MOSH-Insa-Toulouse/2025-2026-4GP-CHAUPIN-ADJASSE/LTSPICE/symb_ampli.png

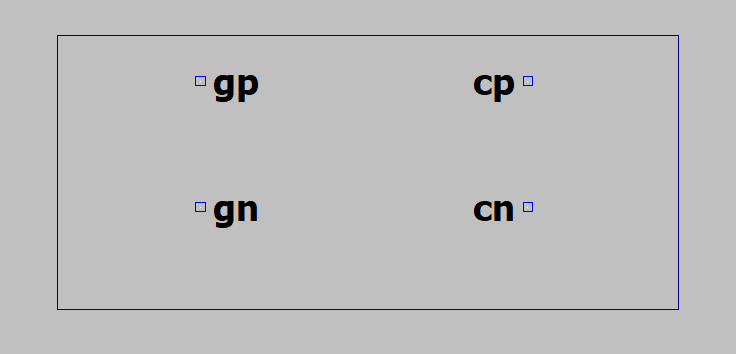
LTSPICE/symb_ampli.png
