MOSH-Insa-Toulouse/2025-2026-4GP-CHAUPIN-ADJASSE/LTSPICE/symb_full.png

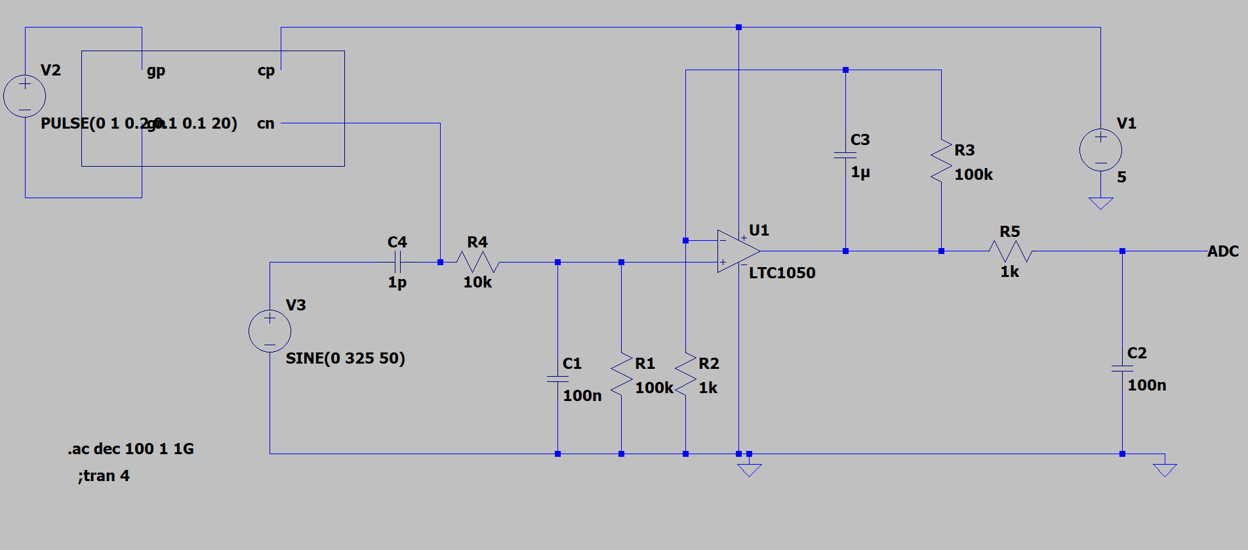
LTSPICE/symb_full.png
