MOSH-Insa-Toulouse/2025-2026-4GP-CHAUPIN-ADJASSE/MIT_APP_INVENTOR/blocs2.png

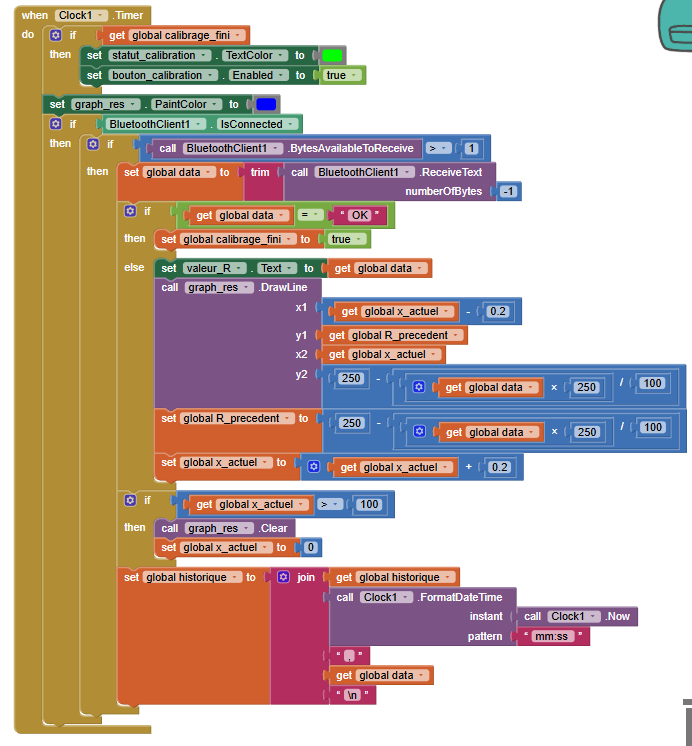
MIT_APP_INVENTOR/blocs2.png
