MOSH-Insa-Toulouse/2025-2026-4GP-CHAUPIN-ADJASSE/MIT_APP_INVENTOR/config_face_avant2.png

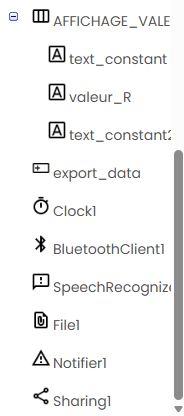
MIT_APP_INVENTOR/config_face_avant2.png
