MOSH-Insa-Toulouse/2025-2026-4GP-CHAUPIN-ADJASSE/Photos_Captures/capture_schema.png

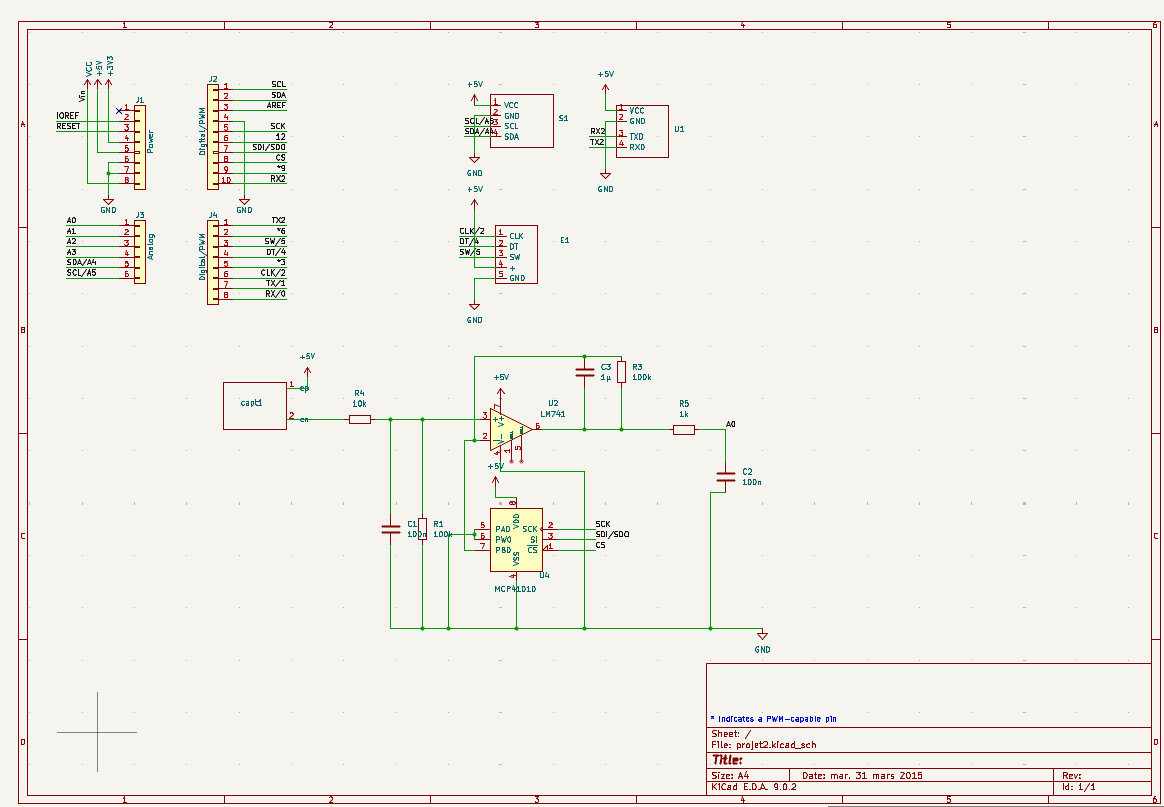
Photos_Captures/capture_schema.png
