MOSH-Insa-Toulouse/2025-2026-4GP-CHAUPIN-ADJASSE/LTSPICE/Draft3.asc

C1: cap; 100n
C2: cap; 100n
C3: cap; 1µ
C4: cap; 1p
R1: res; 100k
R2: res; 1k
R3: res; 100k
R4: res; 10k
R5: res; 1k
U1: LTC1050
V1: voltage; 5
V2: voltage; PULSE(0 1 0.2 0.1 0.1 20)
V3: voltage; SINE(0 325 50)
X1: symb_capteur
Named nets: 0, ADC
;tran 4
.ac dec 100 1 1G
