MOSH-Insa-Toulouse/2025-2026-4GP-CHAUPIN-ADJASSE/LTSPICE/symb_capteur.asc

B1: bi; I=V(cp,cn)*(10n+v(gc,gn)*10n)
C1: cap
R1: res
Named nets: cp, cn, gp, gn, gc
